EIectron/ExpressLRS-Ranger-Modul/IMAGEs/assets/20241106_085437.jpg

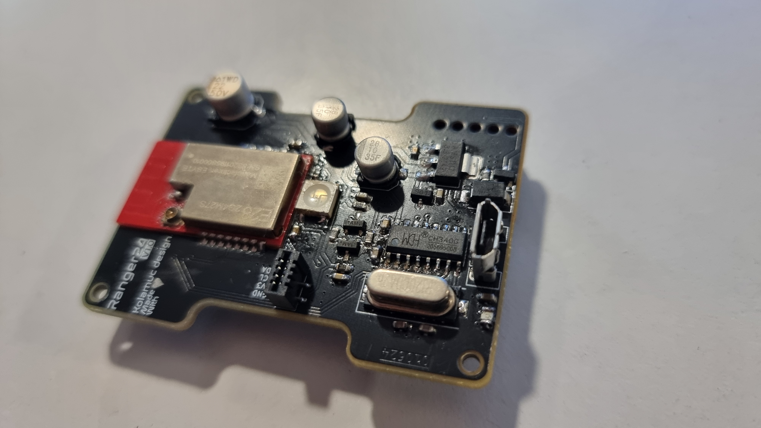
IMAGEs/assets/20241106_085437.jpg
