EIectron/ExpressLRS-Ranger-Modul/IMAGEs/assets/20241106_085519.jpg

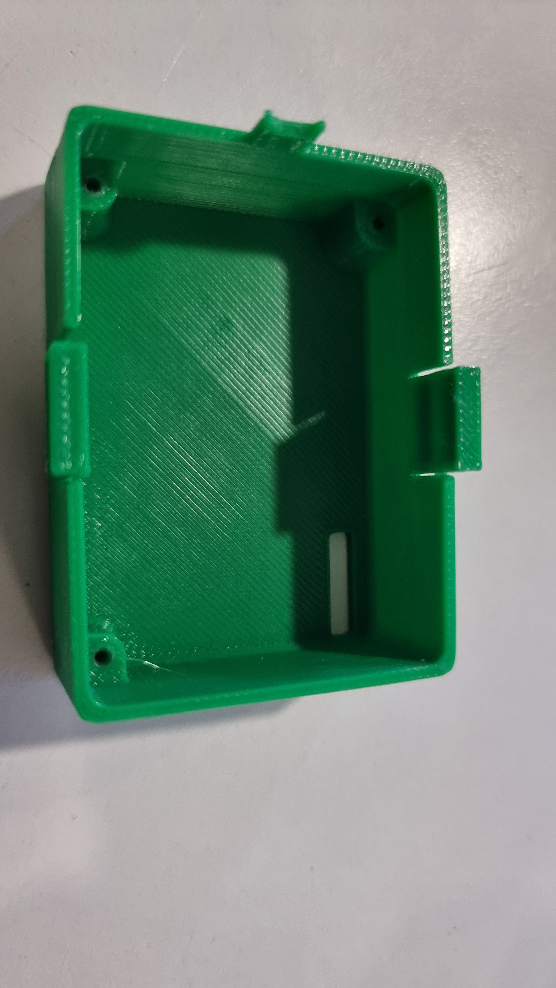
IMAGEs/assets/20241106_085519.jpg
