EIectron/ExpressLRS-Ranger-Modul/IMAGEs/assets/20241106_085652.jpg

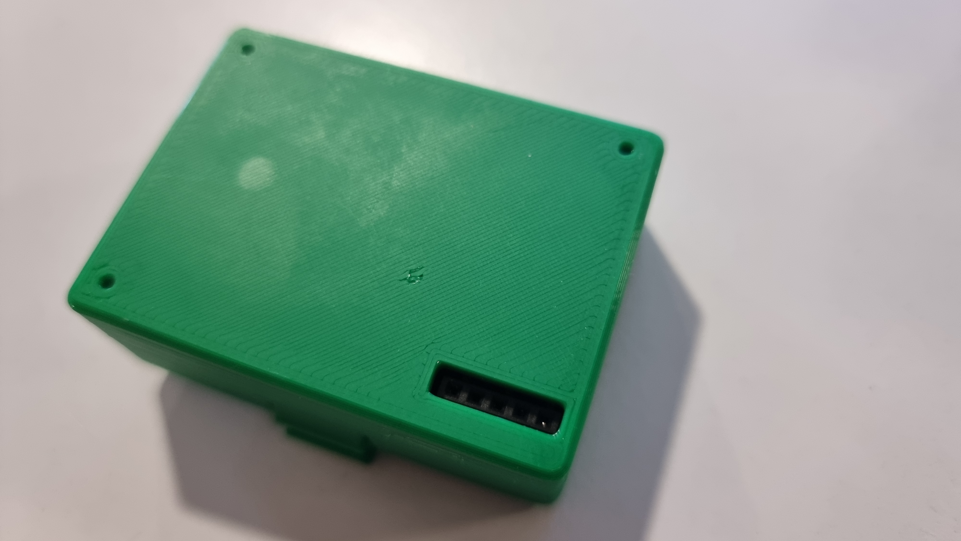
IMAGEs/assets/20241106_085652.jpg
