EIectron/ExpressLRS-Ranger-Modul/IMAGEs/assets/20241106_085716.jpg

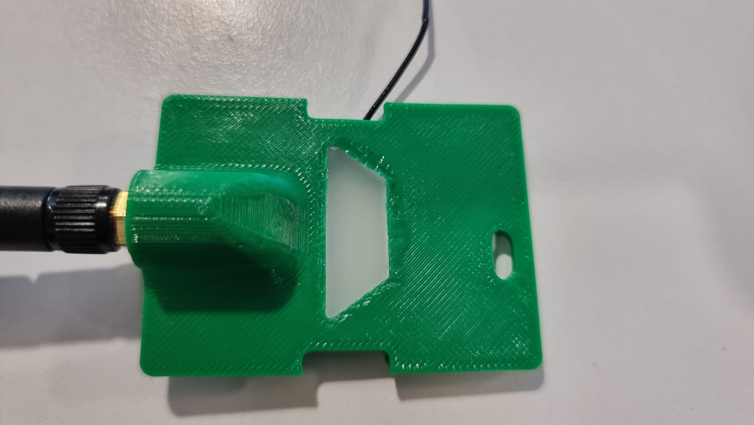
IMAGEs/assets/20241106_085716.jpg
